MotorDynamicsLab/PositronHardware/PositronV3.2/Hardware/LDO Positron Mainboard/LDO Positron Mainboard Rev1.1_3D Layout Top.jpg

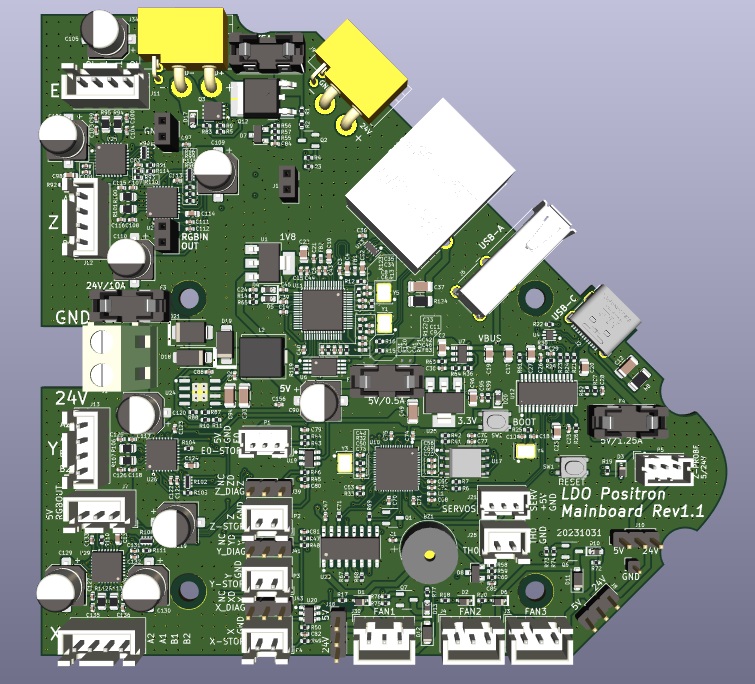
PositronV3.2/Hardware/LDO Positron Mainboard/LDO Positron Mainboard Rev1.1_3D Layout Top.jpg
