MotorDynamicsLab/PositronHardware/PositronV3.2/Hardware/PV3 Switch Board/PV3 Switch PCB Ver1.1_3D Layout Top.jpg

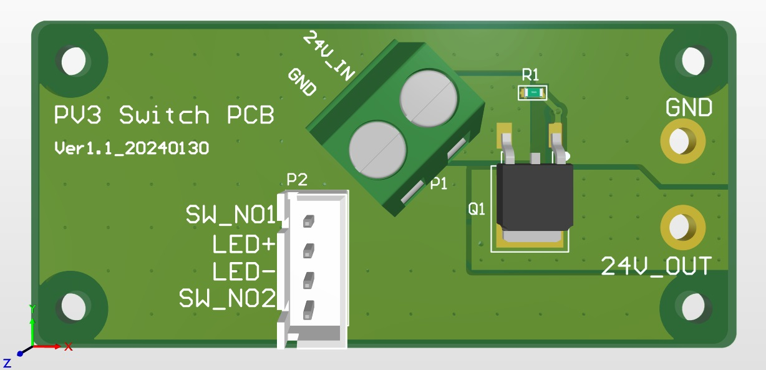
PositronV3.2/Hardware/PV3 Switch Board/PV3 Switch PCB Ver1.1_3D Layout Top.jpg
