MotorDynamicsLab/PositronHardware/PositronV3.2/Configs/sensorless_homing_pv3.cfg

## This file contains configuration and macros pertaining to sensorless homing for Positron V3.2
## It is based on this guide: https://docs.vorondesign.com/community/howto/clee/sensorless_xy_homing.html

## *MAKE SURE* to include this config file *AFTER* the main controller config. 
## This will ensure the relavent sections are overwritten by the configurations specified here.

[stepper_x]
endstop_pin: tmc2209_stepper_x:virtual_endstop
homing_speed: 40
homing_retract_dist: 0

[tmc2209 stepper_x]
diag_pin: ^gpio16
driver_SGTHRS: 48  #Tune this, use the highest value that will not cause a false trigger

[stepper_y]
endstop_pin: tmc2209_stepper_y:virtual_endstop
homing_speed: 40
homing_retract_dist: 0

[tmc2209 stepper_y]
diag_pin: ^gpio25
driver_SGTHRS: 48  #Tune this, use the highest value that will not cause a false trigger

[gcode_macro _HOME_X]
gcode:
    # Always use consistent run_current on A/B steppers during sensorless homing
    {% set RUN_CURRENT_X = printer.configfile.settings['tmc2209 stepper_x'].run_current|float %}
    {% set RUN_CURRENT_Y = printer.configfile.settings['tmc2209 stepper_y'].run_current|float %}
    {% set HOME_CURRENT = 0.7 %}
    SET_TMC_CURRENT STEPPER=stepper_x CURRENT={HOME_CURRENT}
    SET_TMC_CURRENT STEPPER=stepper_y CURRENT={HOME_CURRENT}
    SAVE_GCODE_STATE NAME=STATE_HOME_X

    # Home
    G28 X
    # Move away
    G91
    G1 X5 F1200

    # Wait just a second… (give StallGuard registers time to clear)
    G4 P500
    # Set current during print
    SET_TMC_CURRENT STEPPER=stepper_x CURRENT={RUN_CURRENT_X}
    SET_TMC_CURRENT STEPPER=stepper_y CURRENT={RUN_CURRENT_Y}
    RESTORE_GCODE_STATE NAME=STATE_HOME_X

[gcode_macro _HOME_Y]
gcode:
    # Set current for sensorless homing
    {% set RUN_CURRENT_X = printer.configfile.settings['tmc2209 stepper_x'].run_current|float %}
    {% set RUN_CURRENT_Y = printer.configfile.settings['tmc2209 stepper_y'].run_current|float %}
    {% set HOME_CURRENT = 0.7 %}
    SET_TMC_CURRENT STEPPER=stepper_x CURRENT={HOME_CURRENT}
    SET_TMC_CURRENT STEPPER=stepper_y CURRENT={HOME_CURRENT}
    SAVE_GCODE_STATE NAME=STATE_HOME_Y

    # Home
    G28 Y
    # Move away
    G91
    G1 Y-5 F1200
    
    # Wait just a second… (give StallGuard registers time to clear)
    G4 P500
    # Set current during print
    SET_TMC_CURRENT STEPPER=stepper_x CURRENT={RUN_CURRENT_X}
    SET_TMC_CURRENT STEPPER=stepper_y CURRENT={RUN_CURRENT_Y}
    RESTORE_GCODE_STATE NAME=STATE_HOME_Y


[gcode_macro LIFT_Z]
gcode:
    QUERY_ENDSTOPS
    {% if printer.query_endstops.last_query["z"] %}
        G91
        G1 Z30
    {% endif %}


[homing_override]
axes: xyz
set_position_z: 0
gcode:
    {% set home_all = 'X' not in params and 'Y' not in params and 'Z' not in params %}
    SAVE_GCODE_STATE NAME=STATE_HOME_OVERRIDE

    {% if home_all or 'Y' in params or 'X' in params or 'Z' in params %}
        QUERY_ENDSTOPS
        LIFT_Z
    {% endif %}

    G90
    {% if home_all or 'Y' in params %}
        _HOME_Y
        G0 Y60 F3600
    {% endif %}

    {% if home_all or 'X' in params %}
        _HOME_X
        G0 X40 F3600
    {% endif %}
    
    G28 Z
    G91
    G1 Z10
    RESTORE_GCODE_STATE NAME=STATE_HOME_OVERRIDE
